BiancanielloLeo/APSC200_ProjectDevelopment_2026/Software/Computer Vision/4x4_50 ArUcos/aruco10.png

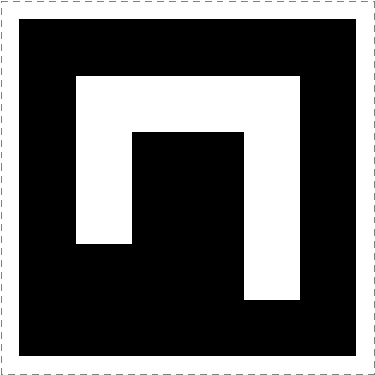
Software/Computer Vision/4x4_50 ArUcos/aruco10.png
