BiancanielloLeo/APSC200_ProjectDevelopment_2026/Software/Computer Vision/4x4_50 ArUcos/aruco11.png

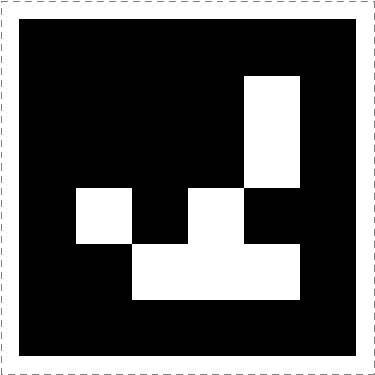
Software/Computer Vision/4x4_50 ArUcos/aruco11.png
